BrettHallen/Commodore_VIC20/VIC-20_DIN-to-S-Video/ENG_CD_5749230_O.pdf

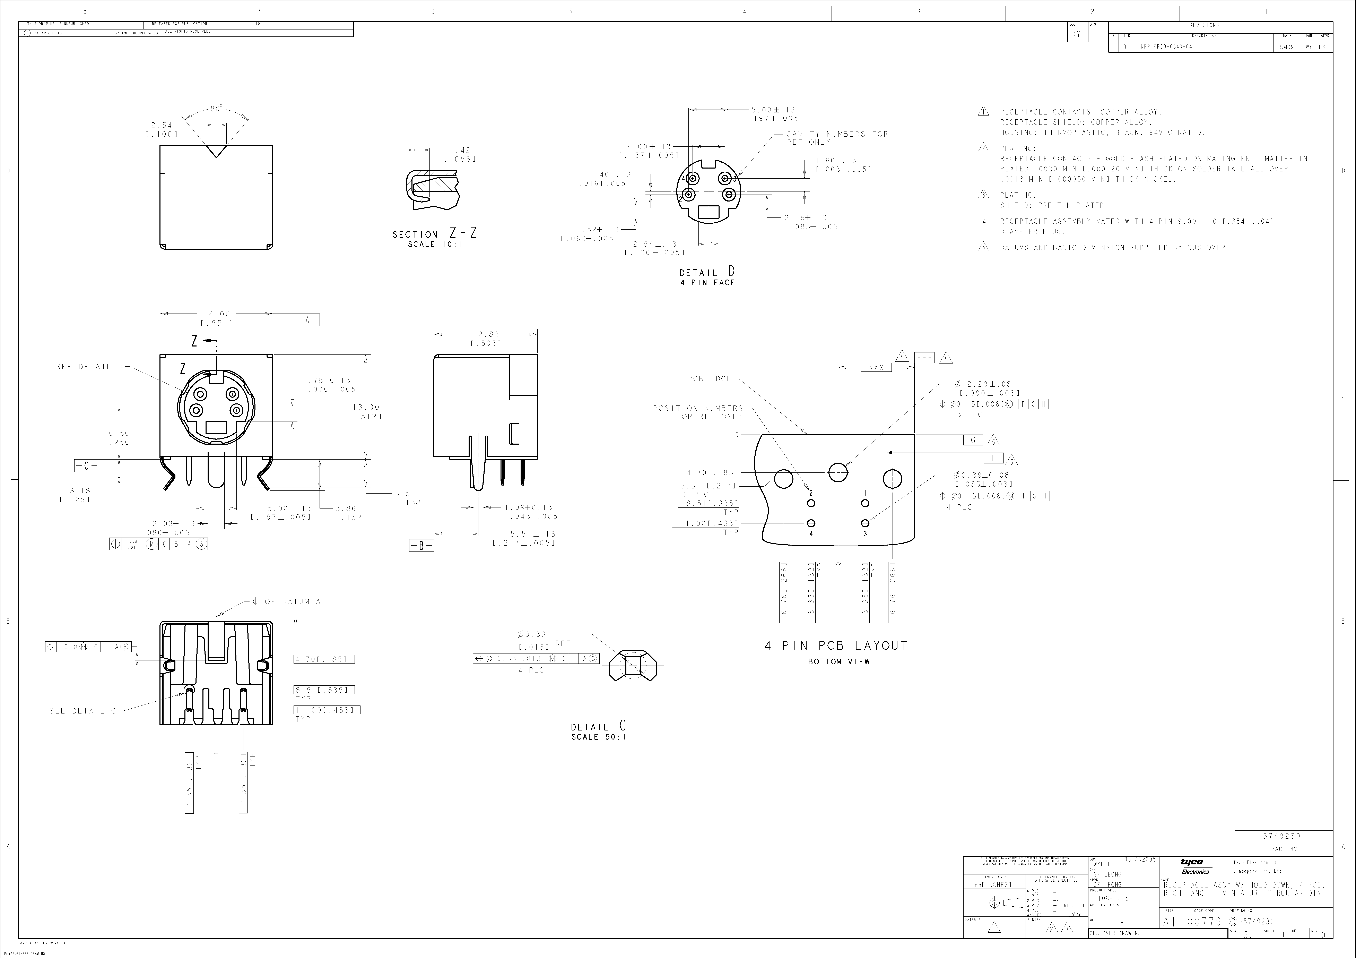
[picture p6: page 1]
