BrettHallen/Commodore_VIC20/Internal_8KB_Simple/VIC-20_Internal_8KB_RAM_Simple.pdf

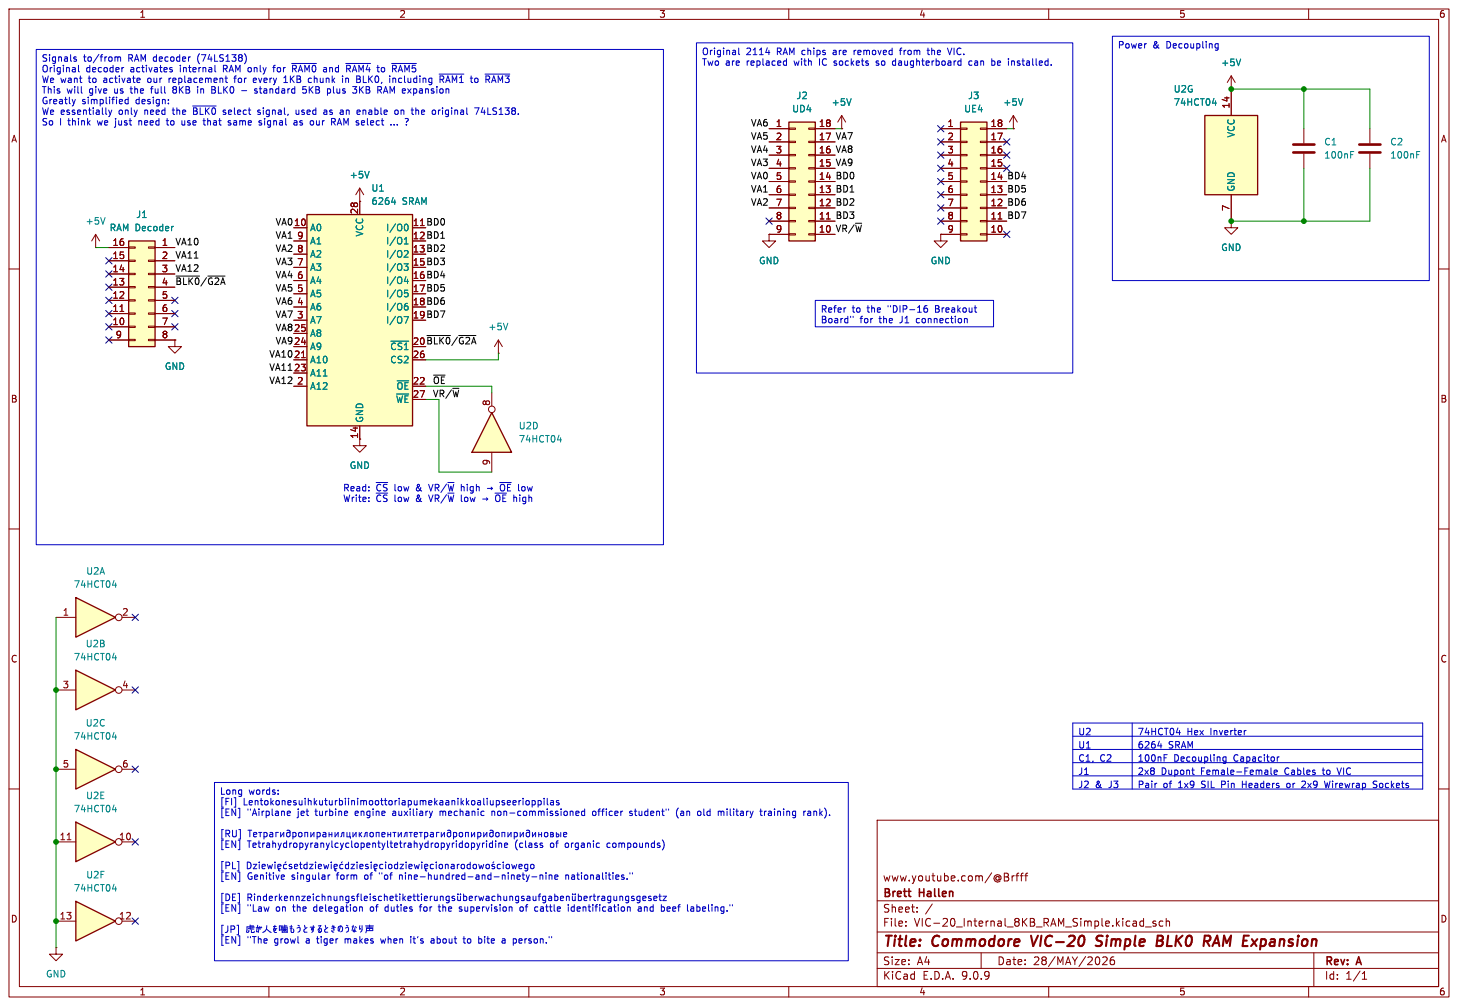
[picture p16: page 1]

[JP] þÿ†N0LNº0’V[0‚0F0h0Y0‹0h0M0n0F0j0ŠXð
[EN] "The growl a tiger makes when it's about to bite a person."
